MrCrusty/APPLE-SLOT-EXTENDER/jpg/IMG_2066.JPG

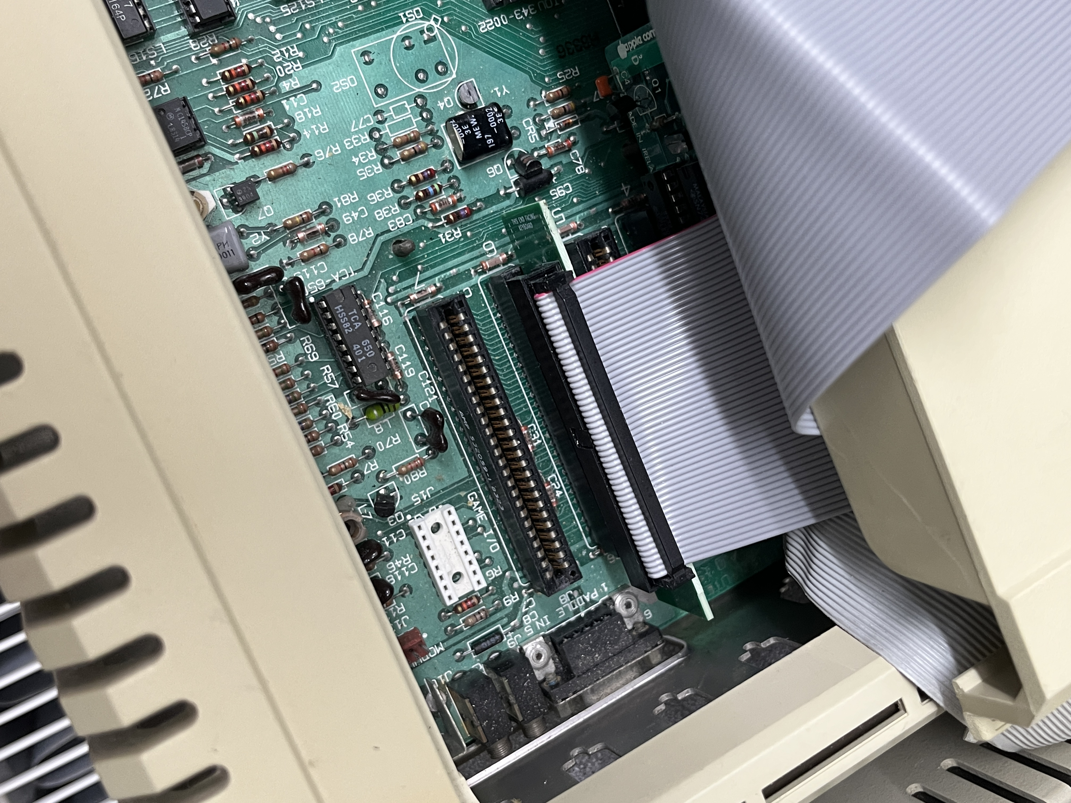
jpg/IMG_2066.JPG
