MrCrusty/APPLE-SLOT-EXTENDER/jpg/IMG_2068.JPG

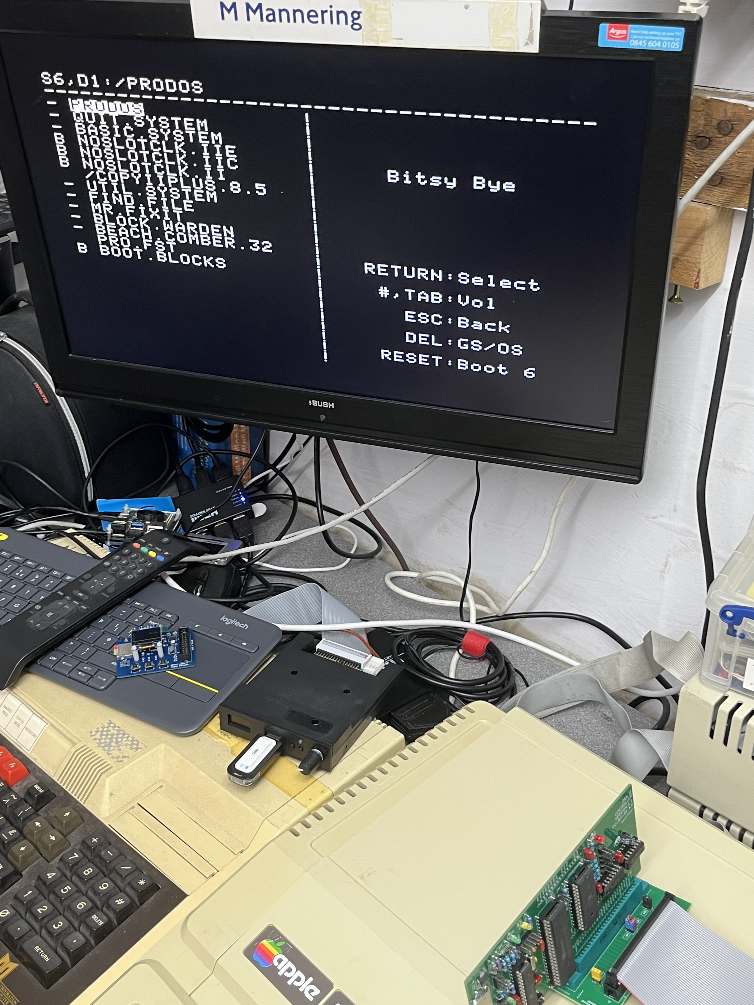
jpg/IMG_2068.JPG
