MrCrusty/APPLE-SLOT-EXTENDER/jpg/IMG_2063.JPG

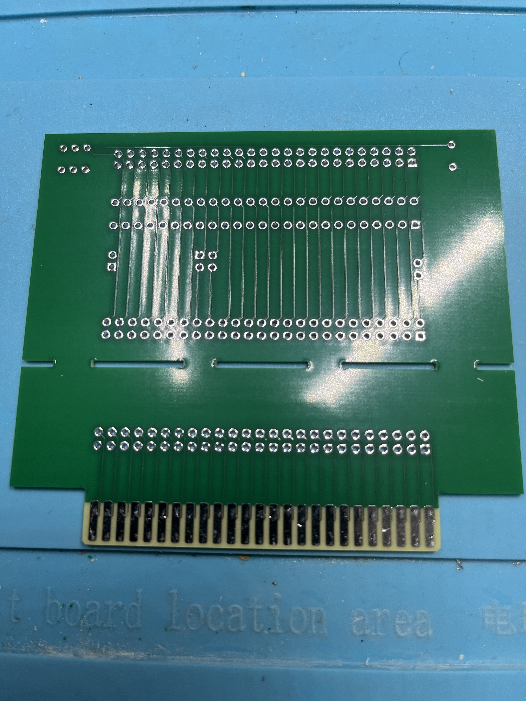
jpg/IMG_2063.JPG
