MrCrusty/APPLE-SLOT-EXTENDER/jpg/IMG_2065.JPG

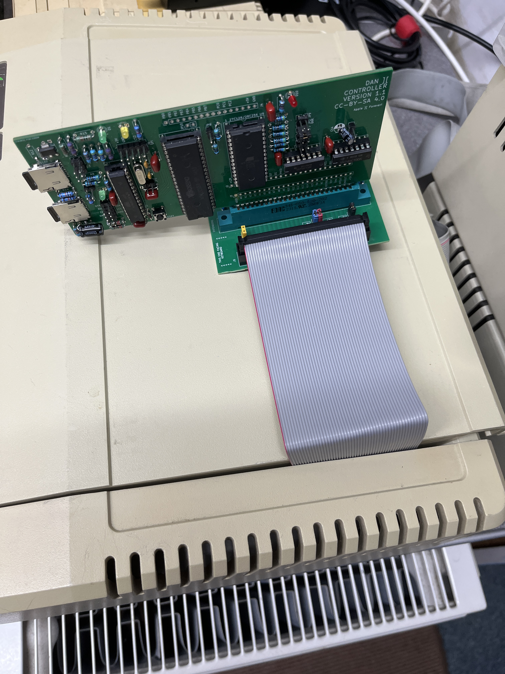
jpg/IMG_2065.JPG
